vanvught/OpenILDA/console-fb/firmware/main.c

/**
 * @file main.c
 *
 */
/* Copyright (C) 2014 by Arjan van Vught <pm @ http://www.raspberrypi.org/forum/>
 *
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
 * THE SOFTWARE IS PROVIDED "AS IS", WITHOUT WARRANTY OF ANY KIND, EXPRESS OR
 * IMPLIED, INCLUDING BUT NOT LIMITED TO THE WARRANTIES OF MERCHANTABILITY,
 * FITNESS FOR A PARTICULAR PURPOSE AND NONINFRINGEMENT. IN NO EVENT SHALL THE
 * AUTHORS OR COPYRIGHT HOLDERS BE LIABLE FOR ANY CLAIM, DAMAGES OR OTHER
 * LIABILITY, WHETHER IN AN ACTION OF CONTRACT, TORT OR OTHERWISE, ARISING FROM,
 * OUT OF OR IN CONNECTION WITH THE SOFTWARE OR THE USE OR OTHER DEALINGS IN
 * THE SOFTWARE.
 */

#include <stdlib.h>
#include <stdio.h>
#include "bcm2835.h"
#include "bcm2835_vc.h"
#include "bcm2835_wdog.h"

void __attribute__((interrupt("IRQ"))) c_irq_handler(void) {}
void __attribute__((interrupt("FIQ"))) c_fiq_handler(void) {}

#ifdef ENABLE_FRAMEBUFFER
#include "fb.h"
#include "console.h"
#else
#include "bcm2835_uart.h"
#endif

extern void cpu_info(void);
extern void mem_info(void);

/**
 *
 * @param boot_dev
 * @param arm_m_type
 * @param atags
 * @return
 */
int notmain(uint32_t boot_dev, uint32_t arm_m_type, uint32_t atags)
{

#ifdef ENABLE_FRAMEBUFFER
	fb_init();
#else
	bcm2835_uart_begin();
#endif

    printf("Compiled on %s at %s\n\n", __DATE__, __TIME__);
    mem_info();
	cpu_info();
	printf("\n");
	printf("EMMC Clock rate (Hz): %ld\n", bcm2835_vc_get_clock_rate(BCM2835_VC_CLOCK_ID_EMMC));
	printf("UART Clock rate (Hz): %ld\n", bcm2835_vc_get_clock_rate(BCM2835_VC_CLOCK_ID_UART));
	printf("ARM  Clock rate (Hz): %ld\n", bcm2835_vc_get_clock_rate(BCM2835_VC_CLOCK_ID_ARM));
	printf("CORE Clock rate (Hz): %ld\n", bcm2835_vc_get_clock_rate(BCM2835_VC_CLOCK_ID_CORE));
	printf("\n");
	printf("Set UART Clock rate 4000000 Hz: %ld\n", bcm2835_vc_set_clock_rate(BCM2835_VC_CLOCK_ID_UART, 4000000));
	printf("UART Clock rate (Hz): %ld\n", bcm2835_vc_get_clock_rate(BCM2835_VC_CLOCK_ID_UART));
	printf("\n");

	uint8_t mac_address[6];
	bcm2835_vc_get_board_mac_address(mac_address);
	printf("MAC address : %.2X:%.2X:%.2X:%.2X:%.2X:%.2X\n", mac_address[0],mac_address[1],mac_address[2],mac_address[3],mac_address[4],mac_address[5]);

	printf("\nProgram ending...\n");

    return 0;
}
